ITManie/led_controller/iqrf/iqrf/IQRF-functions.h

// *********************************************************************
//      				IQRF - definitions file						   *
// *********************************************************************
// Intended for:
//    OS: v3.08D
//
// File:    IQRF-functions.h
// Version: v1.00                                   Revision: 04/02/2016
//
// Revision history:
//   v1.00: 04/02/2016  First release for OS 3.08D.
//
// *********************************************************************
 
#pragma optimize 0
#pragma update_PAGE 0
#pragma update_RP 0

#pragma origin 0x3810
void dummy()
{
  #asm
    DW 0x2000
  #endasm
  #pragma updateBank exit=11
}

#pragma origin 0x3816
void iqrfSleep()
{
  #asm
    DW 0x2000
  #endasm
  #pragma updateBank exit=11
}

#pragma origin 0x3819
void _debug()
{
  #asm
    DW 0x2000
  #endasm
  #pragma updateBank exit=11
}

#define debug()	    \
	do {			\
		_debug();	\
        nop();      \
	} while (0)

#pragma origin 0x381c
void moduleInfo()
{
  #asm
    DW 0x2000
  #endasm
  #pragma updateBank exit=11
}

#pragma origin 0x381f
void appInfo()
{
  #asm
    DW 0x2000
  #endasm
  #pragma updateBank exit=11
}

#pragma origin 0x3822
void pulsingLEDR()
{
  #asm
    DW 0x2000
  #endasm
  #pragma updateBank exit=11
}

#pragma origin 0x3825
void pulseLEDR()
{
  #asm
    DW 0x2000
  #endasm
  #pragma updateBank exit=11
}

#pragma origin 0x3828
void stopLEDR()
{
  #asm
    DW 0x2000
  #endasm
  #pragma updateBank exit=11
}

#pragma origin 0x382b
void pulsingLEDG()
{
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

#pragma origin 0x3931
void setINDF0(char value @ W)
{
  #asm
    DW 0x2000
  #endasm
  #pragma updateBank exit=11
}

#pragma origin 0x3934
void setINDF1(char value @ W)
{
  #asm
    DW 0x2000
  #endasm
  #pragma updateBank exit=11
}

#pragma origin 0x3937
uns8 getRSSI()
{
  #asm
    DW 0x2000
  #endasm
  #pragma updateBank exit=11
  return 1;
}

#pragma origin 0x393a
void removeBondAddress()
{
  #asm
    DW 0x2000
  #endasm
  #pragma updateBank exit=11
}

#pragma origin 0x393d
uns8 sendFRC(char command @ W)
{
  #asm
    DW 0x2000
  #endasm
  #pragma updateBank exit=11
  return 1;
}

#pragma origin 0x3940
void responseFRC()
{
  #asm
    DW 0x2000
  #endasm
  #pragma updateBank exit=11
}

#pragma origin 0x3943
bit bondRequestAdvanced()
{
  #asm
    DW 0x2000
  #endasm
  #pragma updateBank exit=11
  return Carry;
}

#pragma origin 0x3946
bit prebondNode()
{
  #asm
    DW 0x2000
  #endasm
  #pragma updateBank exit=11
  return Carry;
}

#pragma origin 0x3949
bit nodeAuthorization(uns16 mid @ param3, char address @ W)
{
  #asm
    DW 0x2000
  #endasm
  #pragma updateBank exit=11
  return Carry;
}

#pragma origin 0x394c
void dummy01()
{
  #asm
  DW 0x2000
  #endasm
  #pragma updateBank exit=11
}

#pragma origin 0x3961
bit amIRecipientOfFRC()
{
  #asm
    DW 0x2000
  #endasm
  #pragma updateBank exit=11
  return Carry;
}

#pragma optimize 1
#pragma update_RP 1
#pragma update_PAGE 1
#pragma origin __APPLICATION_ADDRESS
